pdbuchan/buscard/docs/assets/gerber/PLEASE_CHAMFER_CARD_EDGES.jpg

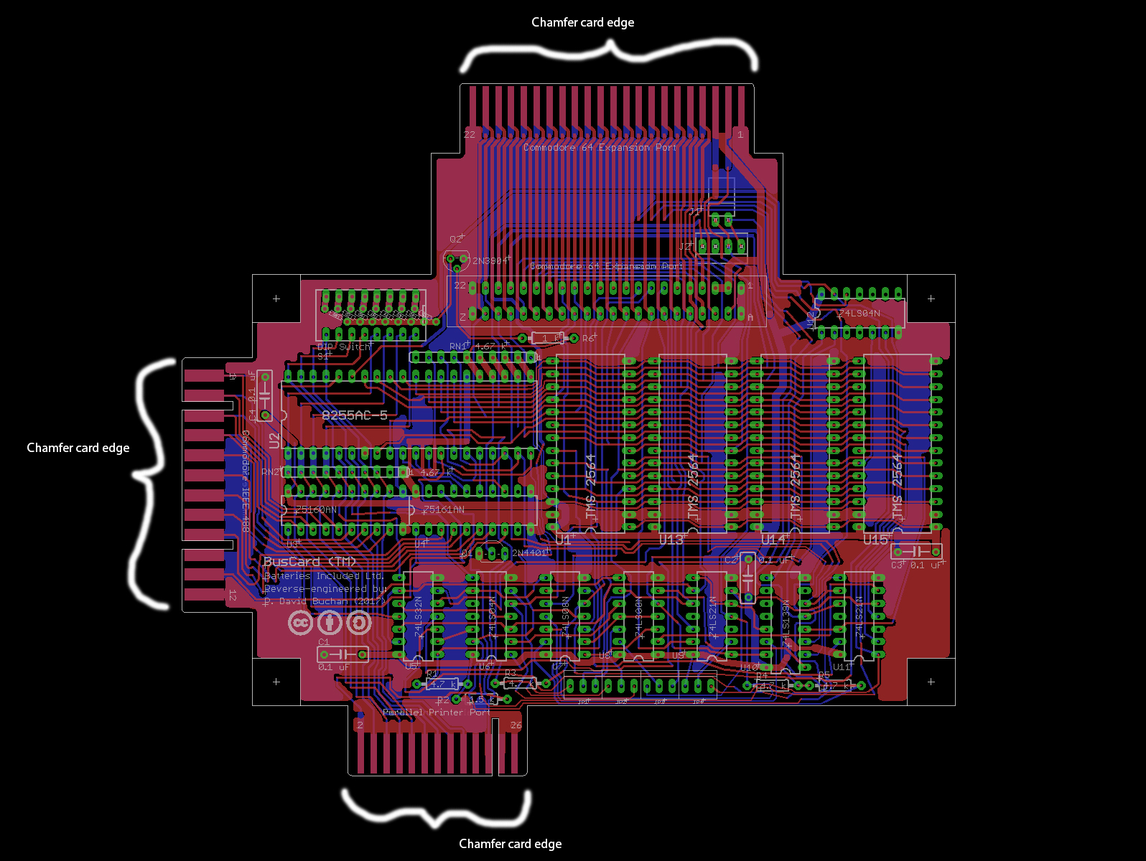
docs/assets/gerber/PLEASE_CHAMFER_CARD_EDGES.jpg
