pdbuchan/buscard/docs/assets/images/bottom.jpg

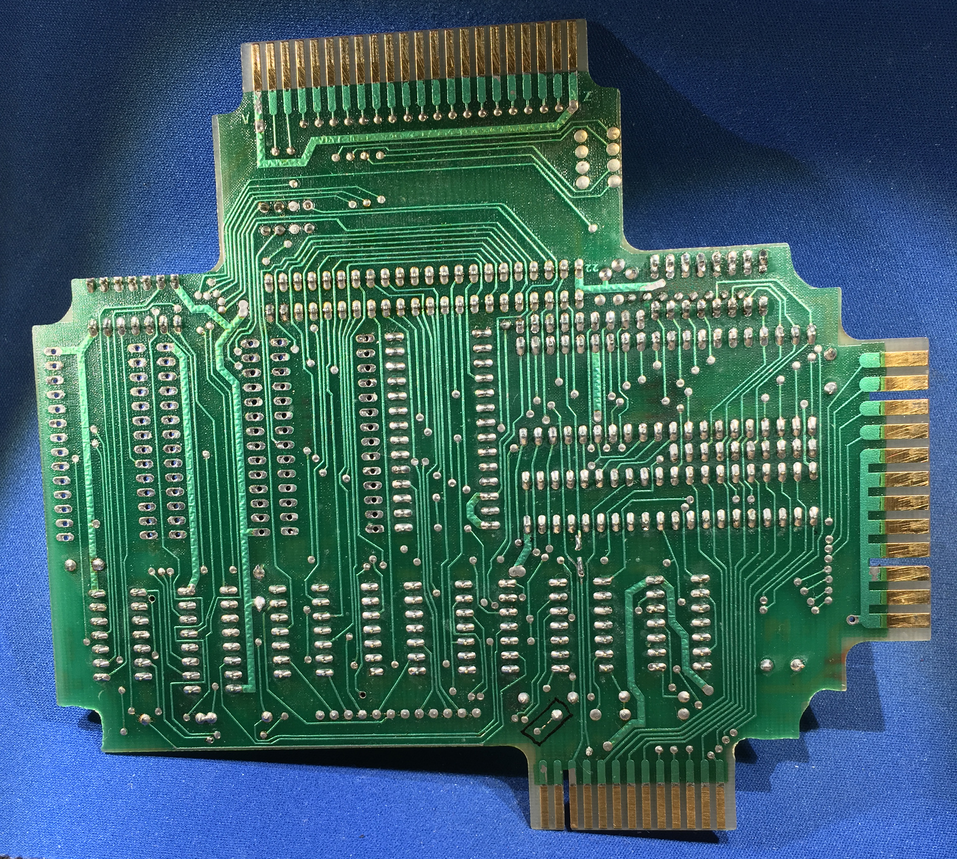
docs/assets/images/bottom.jpg
