pdbuchan/buscard/docs/assets/images/bottom_cover_inside.jpg

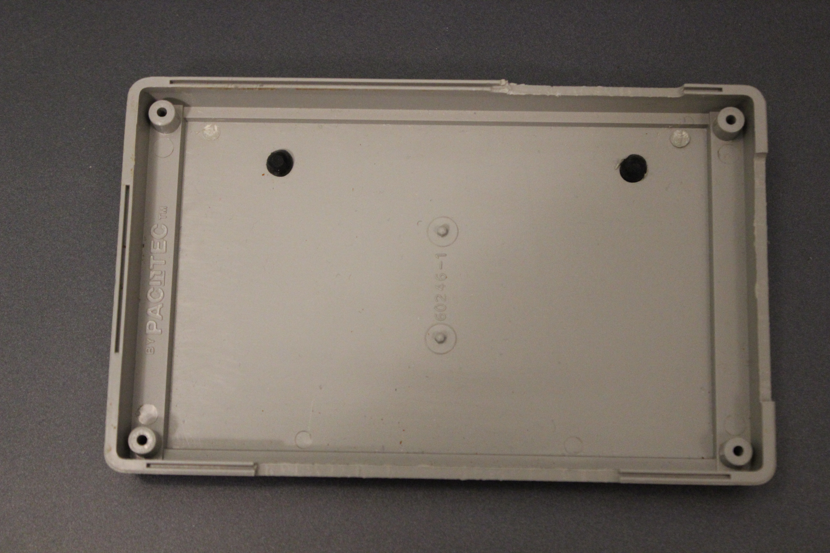
docs/assets/images/bottom_cover_inside.jpg
