pdbuchan/buscard/docs/assets/images/bottom_cover_underside.jpg

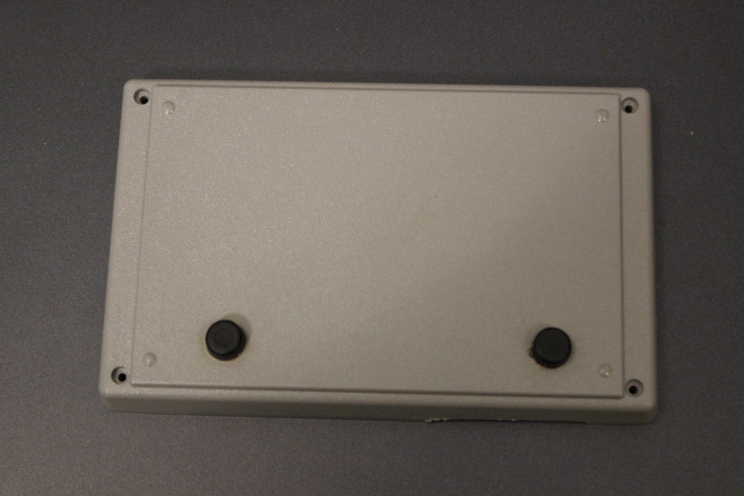
docs/assets/images/bottom_cover_underside.jpg
