pdbuchan/buscard/docs/assets/images/bottom_of_board_backlit.jpg

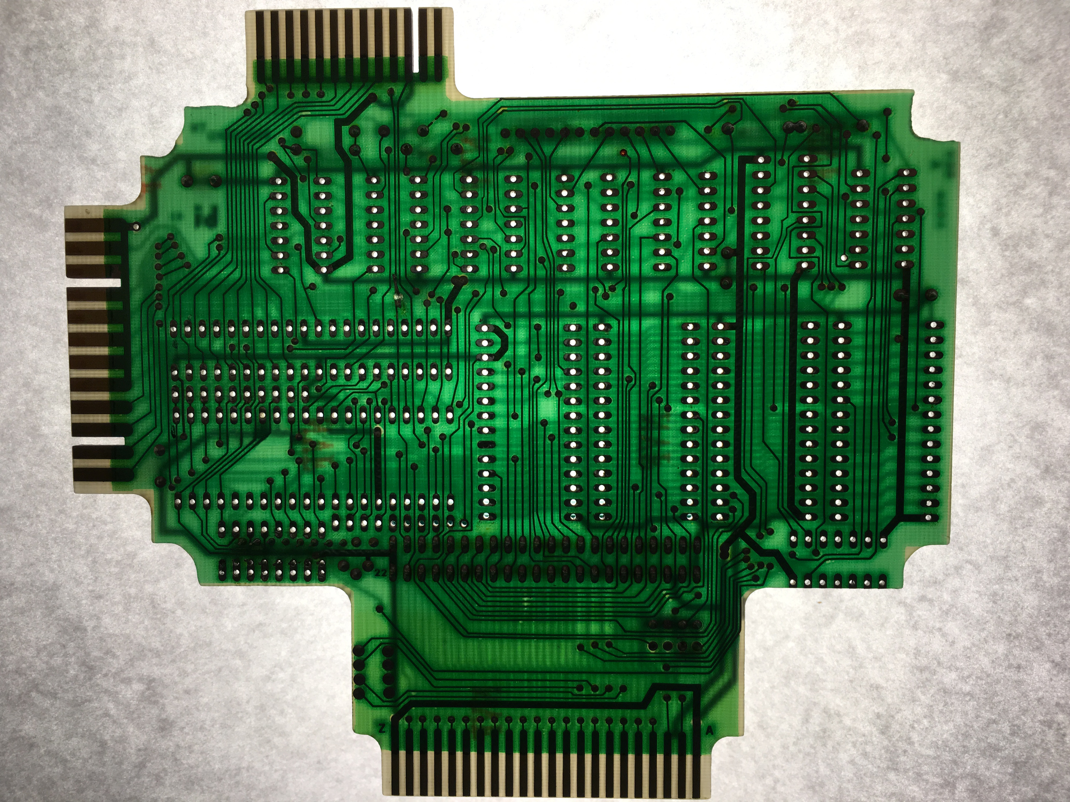
docs/assets/images/bottom_of_board_backlit.jpg
