pdbuchan/buscard/docs/assets/images/clips.jpg

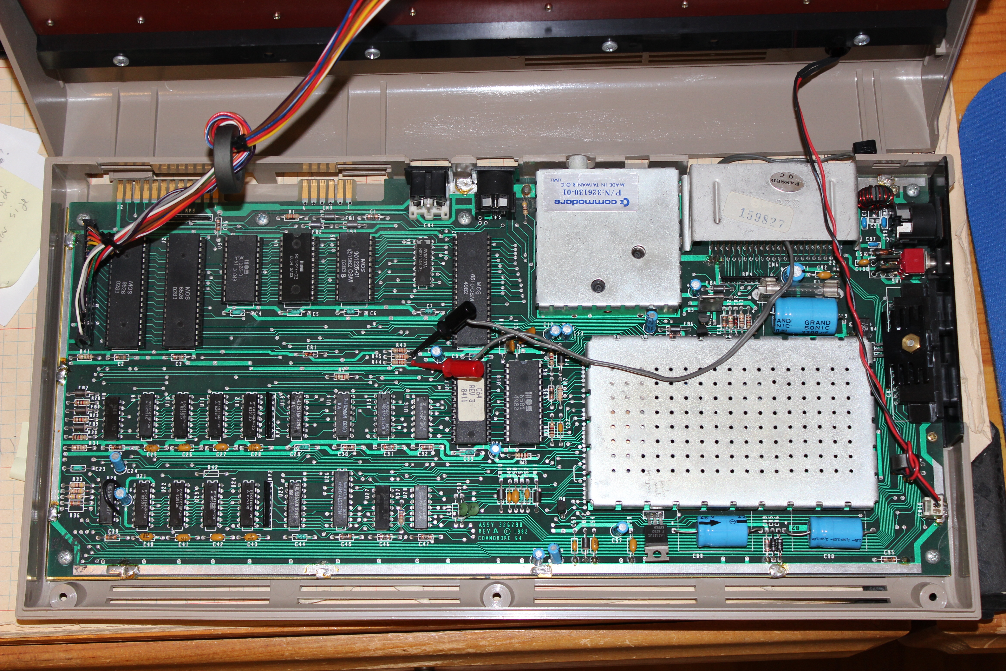
docs/assets/images/clips.jpg
