pdbuchan/buscard/docs/assets/images/diodes-switch_foil_backlit_top.jpg

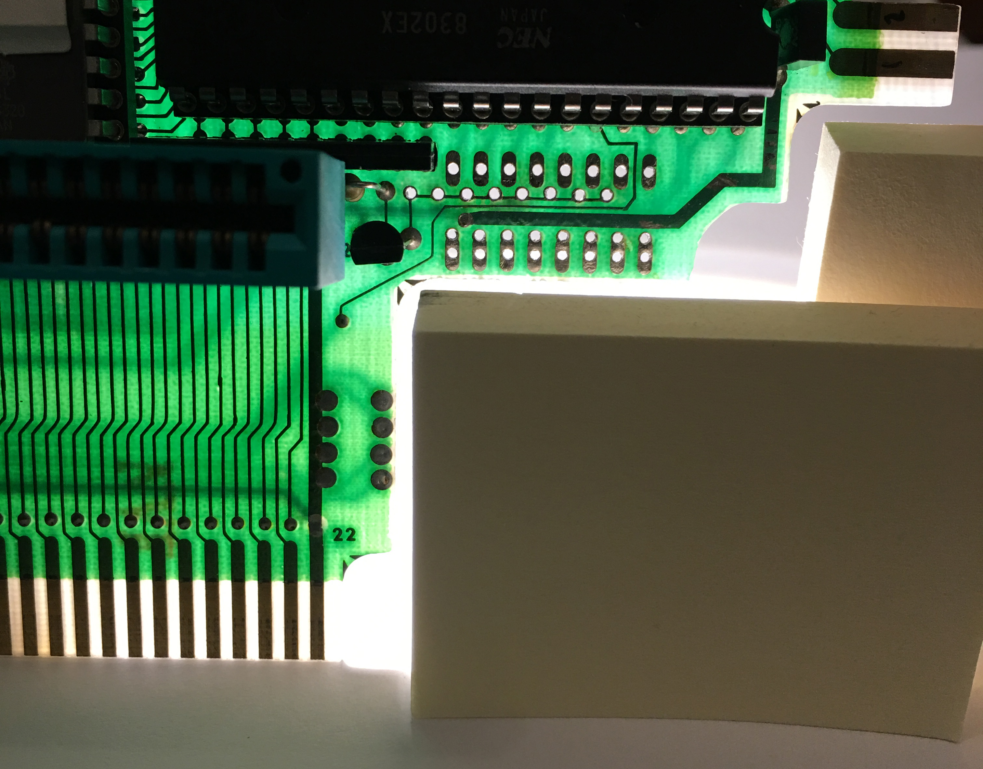
docs/assets/images/diodes-switch_foil_backlit_top.jpg
