pdbuchan/buscard/docs/assets/images/diodes-switch_foil_top.jpg

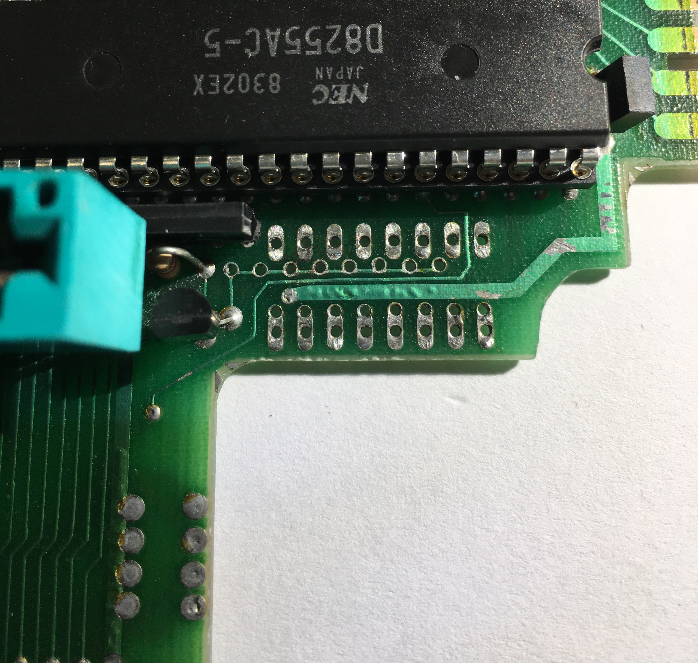
docs/assets/images/diodes-switch_foil_top.jpg
