pdbuchan/buscard/docs/assets/images/diodes.jpg

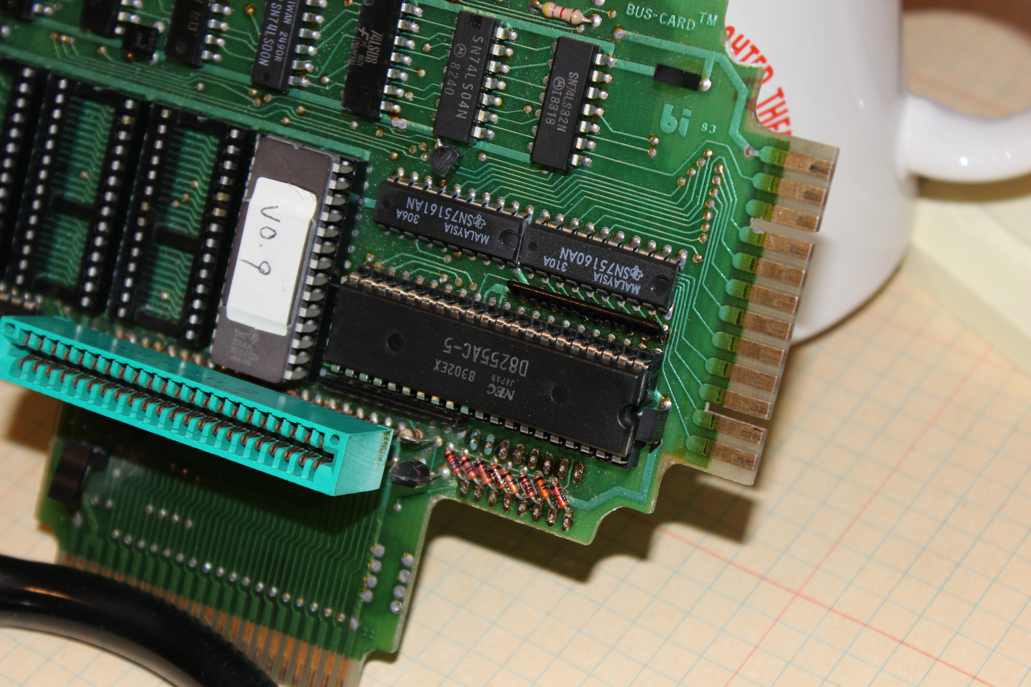
docs/assets/images/diodes.jpg
