pdbuchan/buscard/docs/assets/images/expansion_port_backlit1.jpg

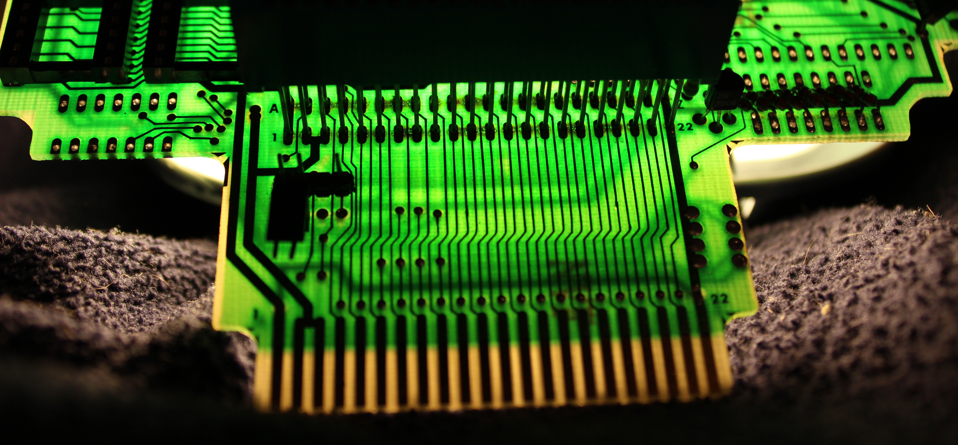
docs/assets/images/expansion_port_backlit1.jpg
