pdbuchan/buscard/docs/assets/images/expansion_port_backlit2.jpg

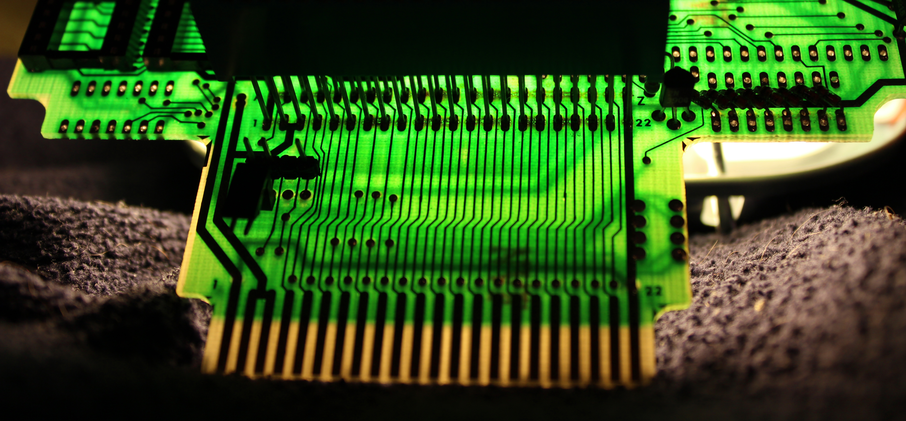
docs/assets/images/expansion_port_backlit2.jpg
