pdbuchan/buscard/docs/assets/images/new_bottom.jpg

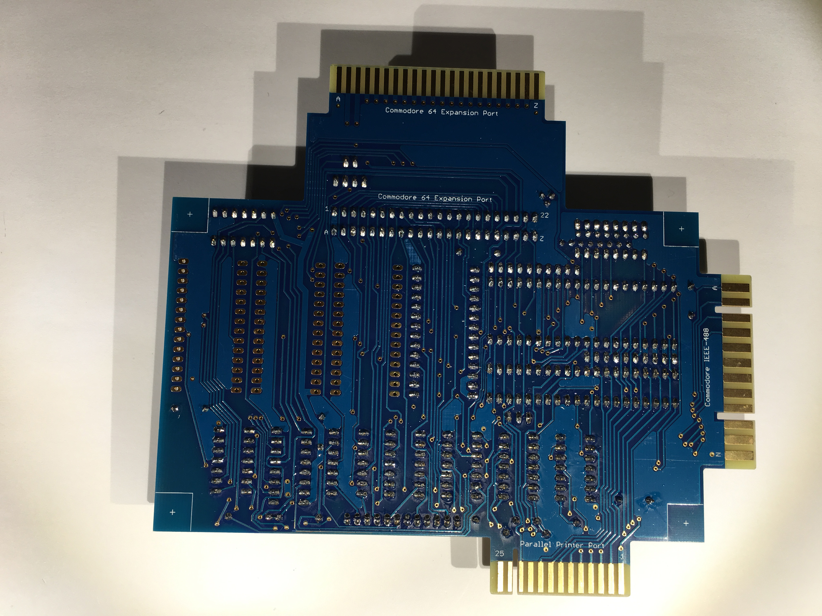
docs/assets/images/new_bottom.jpg
