pdbuchan/buscard/docs/assets/images/new_top1.jpg

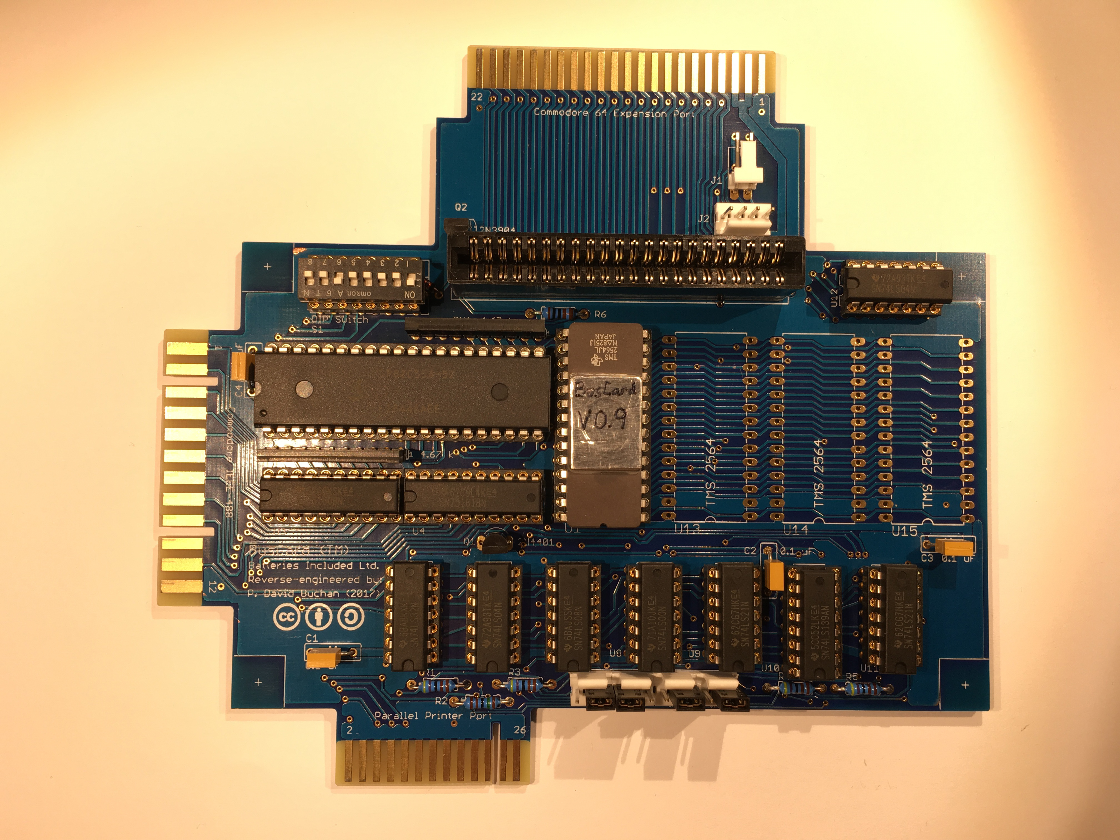
docs/assets/images/new_top1.jpg
