pdbuchan/buscard/docs/assets/images/new_top2.jpg

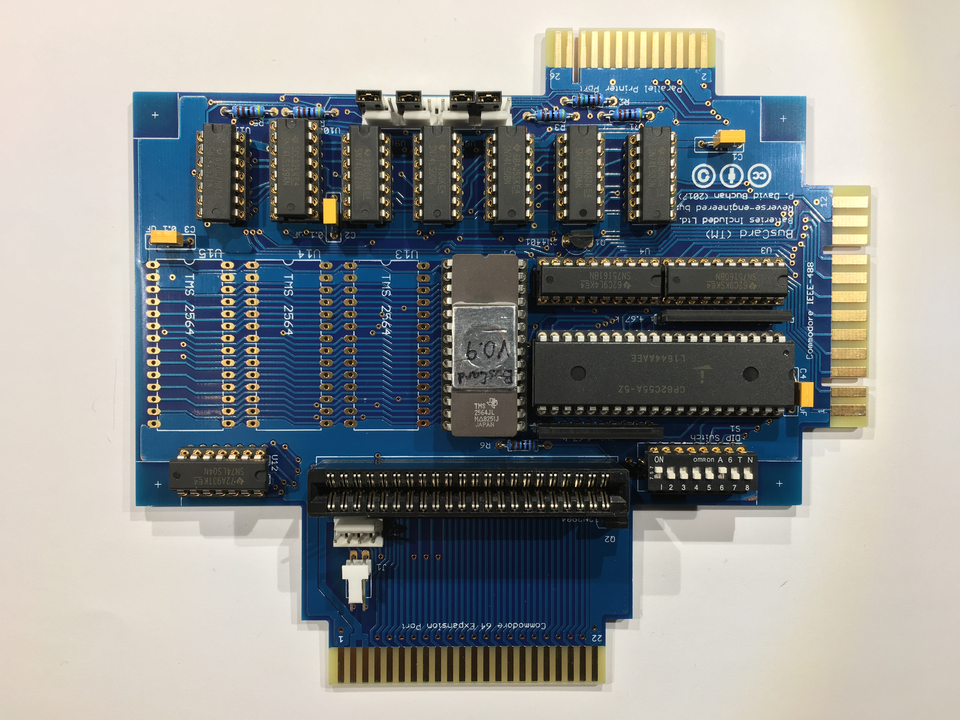
docs/assets/images/new_top2.jpg
