pdbuchan/buscard/docs/assets/images/new_top_no_chips1.jpg

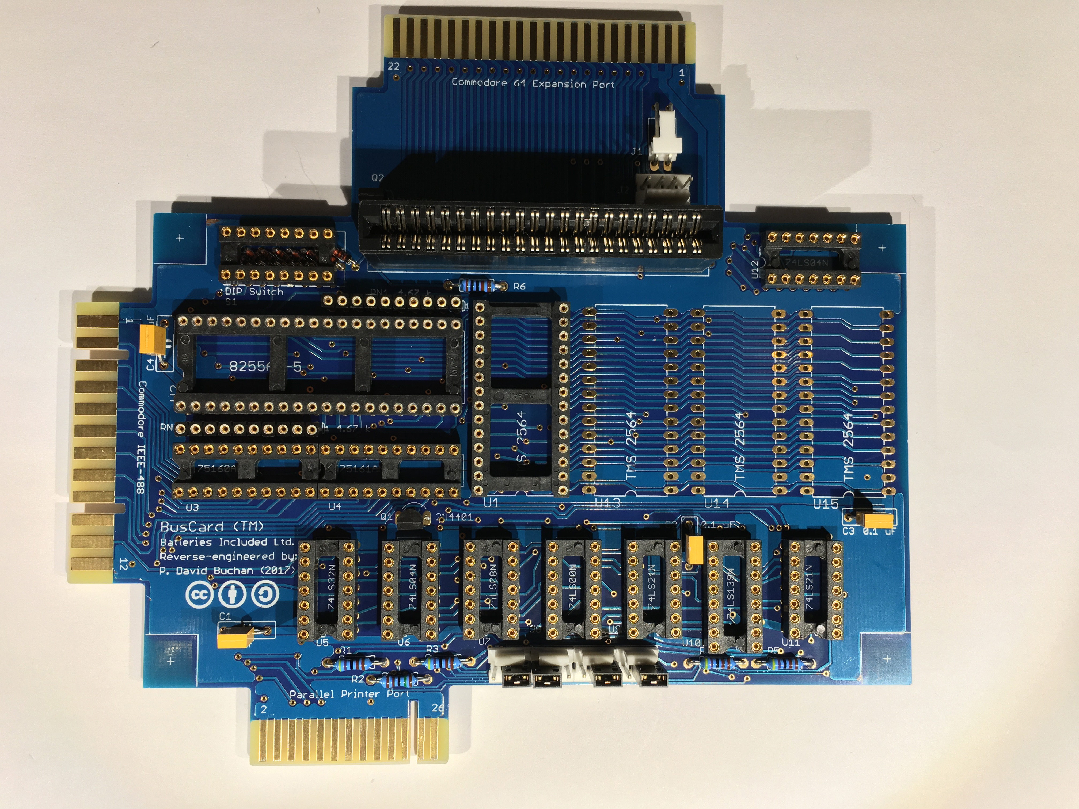
docs/assets/images/new_top_no_chips1.jpg
