pdbuchan/buscard/docs/assets/images/new_top_no_chips2.jpg

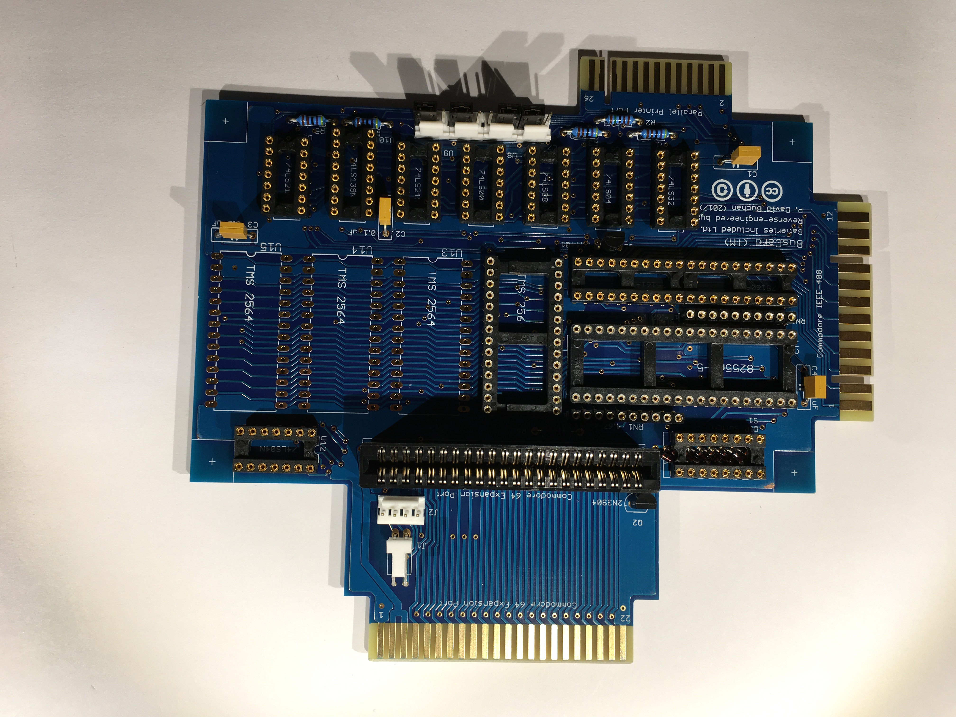
docs/assets/images/new_top_no_chips2.jpg
