pdbuchan/buscard/docs/assets/images/not_plugged_in.jpg

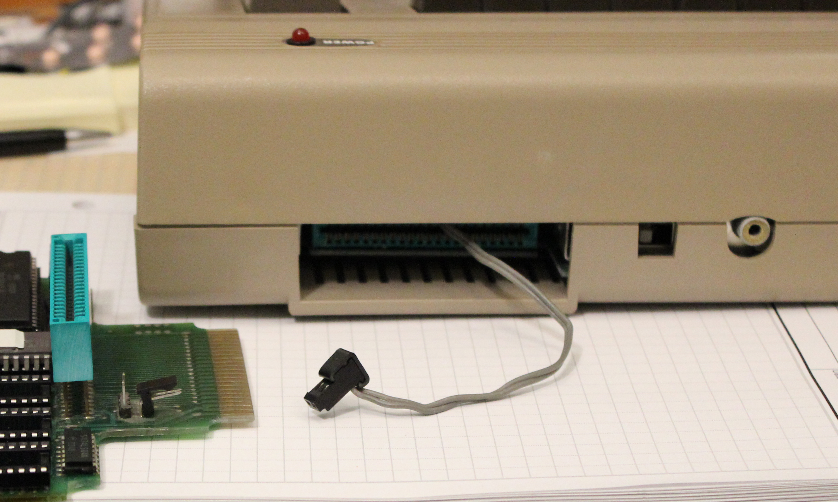
docs/assets/images/not_plugged_in.jpg
