pdbuchan/buscard/docs/assets/images/plugged_in.jpg

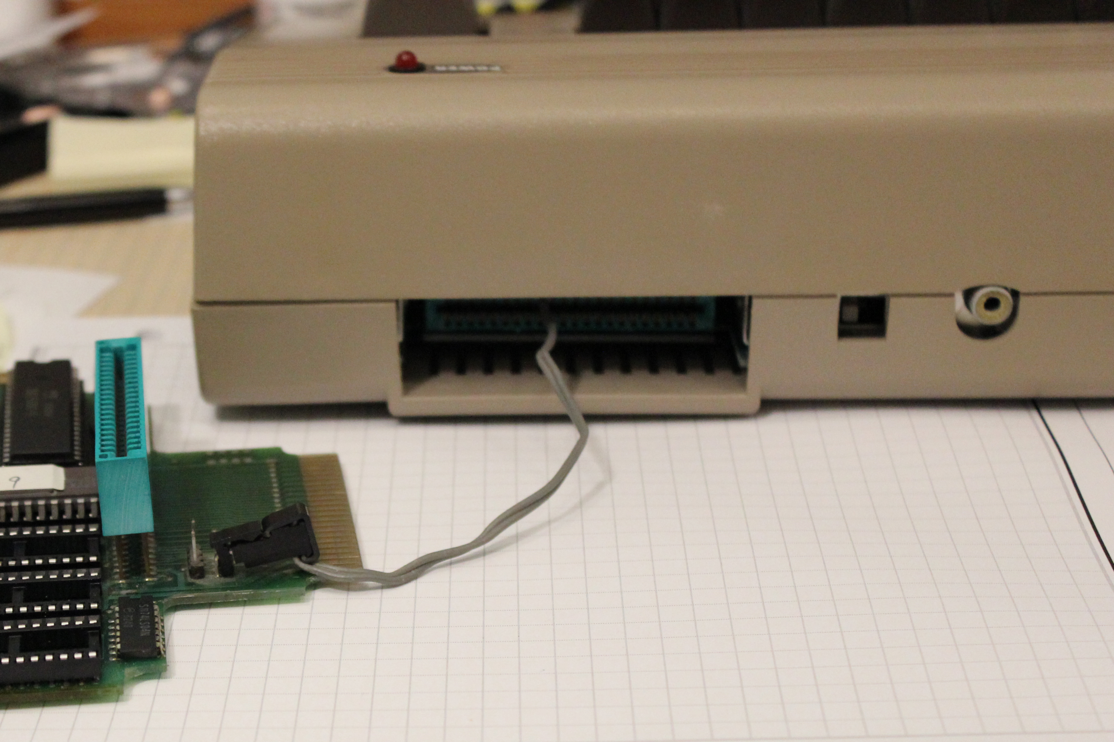
docs/assets/images/plugged_in.jpg
