pdbuchan/buscard/docs/assets/images/side_view01.jpg

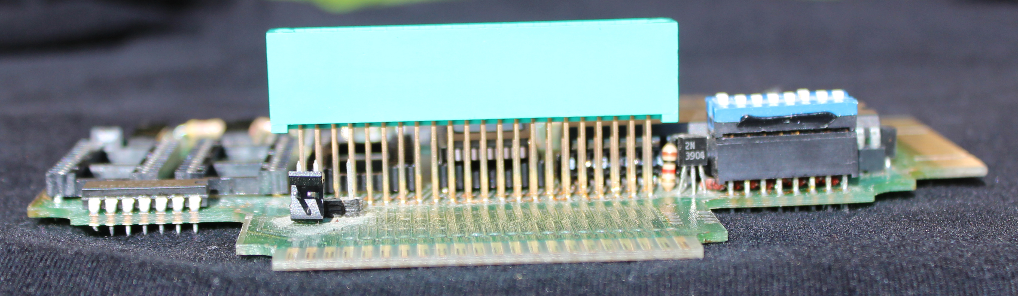
docs/assets/images/side_view01.jpg
