pdbuchan/buscard/docs/assets/images/side_view02.jpg

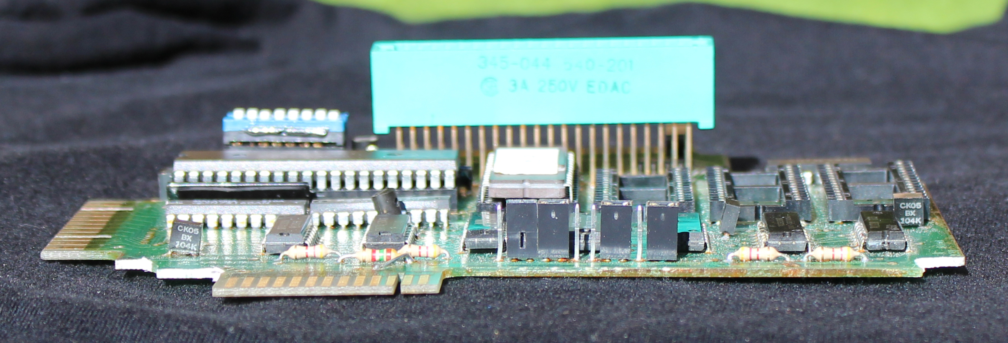
docs/assets/images/side_view02.jpg
