pdbuchan/buscard/docs/assets/images/side_view04.jpg

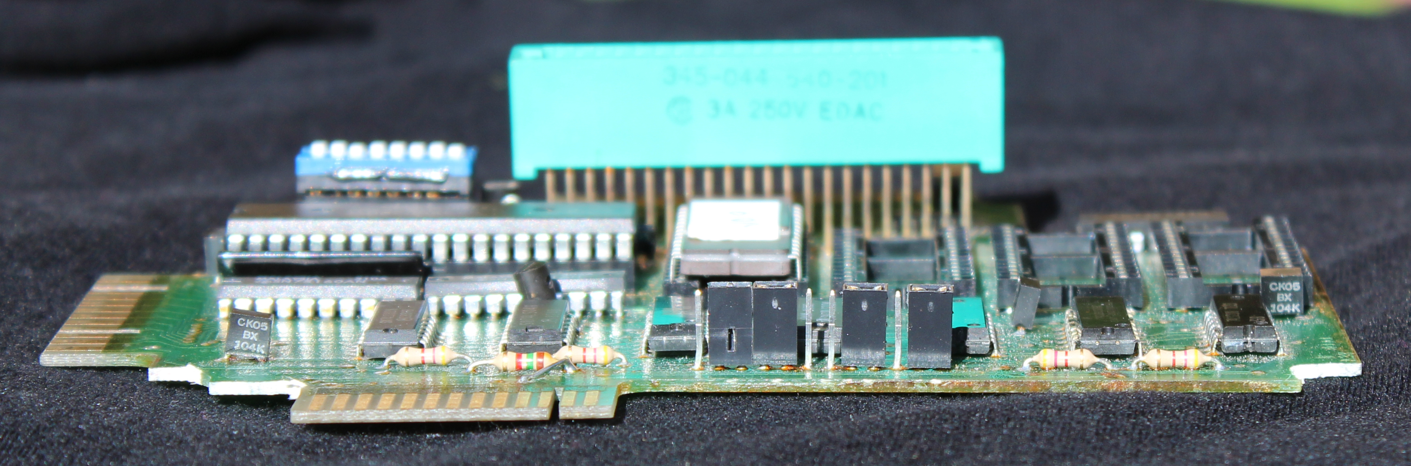
docs/assets/images/side_view04.jpg
