pdbuchan/buscard/docs/assets/images/side_view05.jpg

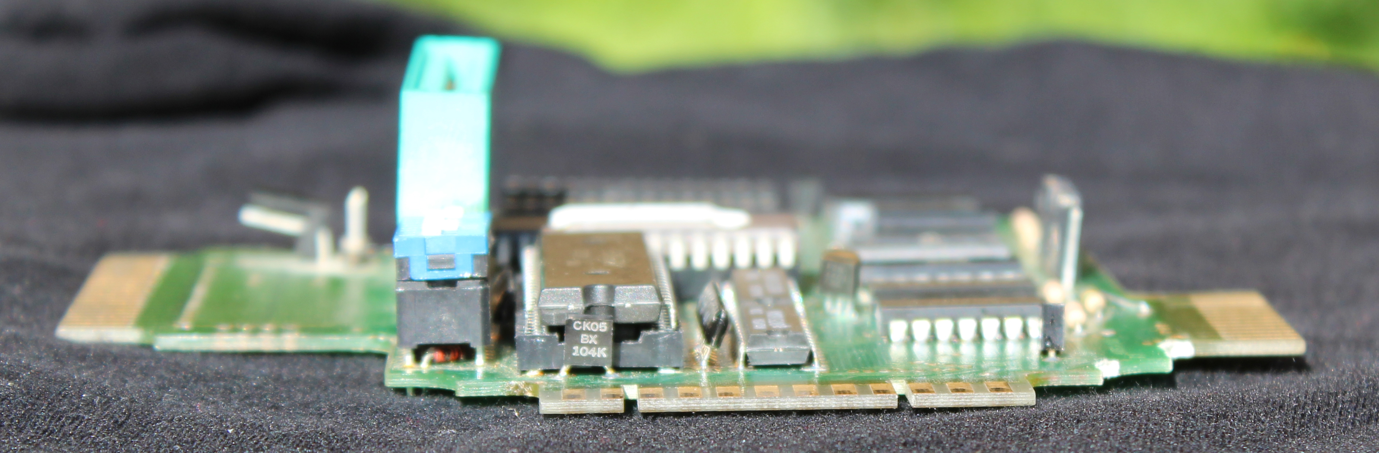
docs/assets/images/side_view05.jpg
