pdbuchan/buscard/docs/assets/images/side_view06.jpg

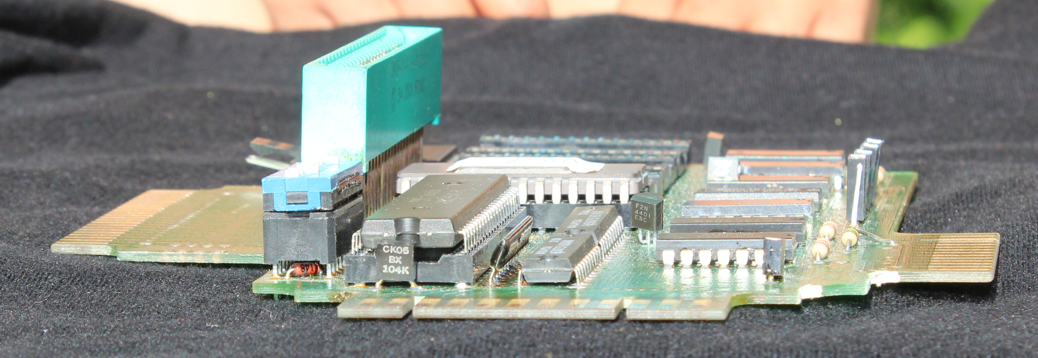
docs/assets/images/side_view06.jpg
