pdbuchan/buscard/docs/assets/images/side_view07.jpg

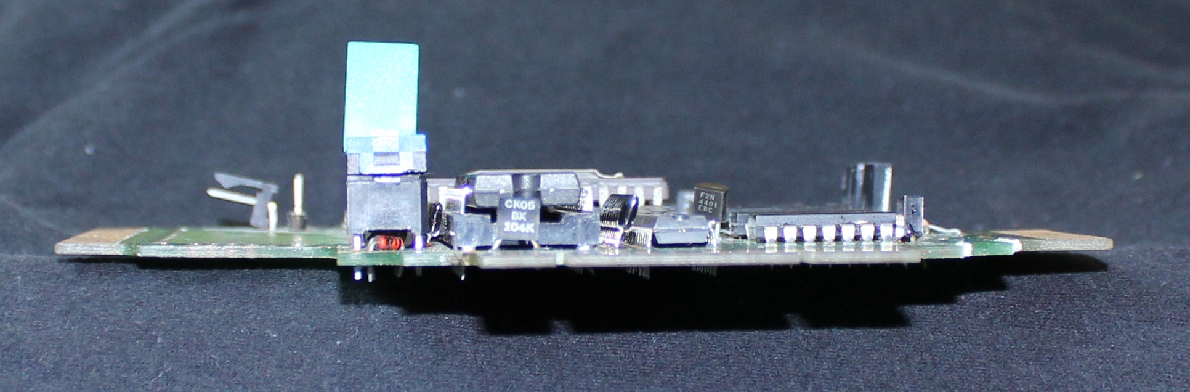
docs/assets/images/side_view07.jpg
