pdbuchan/buscard/docs/assets/images/side_view08.jpg

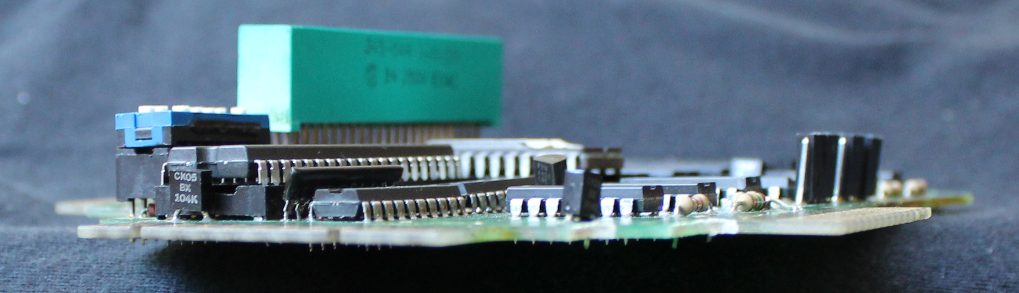
docs/assets/images/side_view08.jpg
