pdbuchan/buscard/docs/assets/images/side_view09.jpg

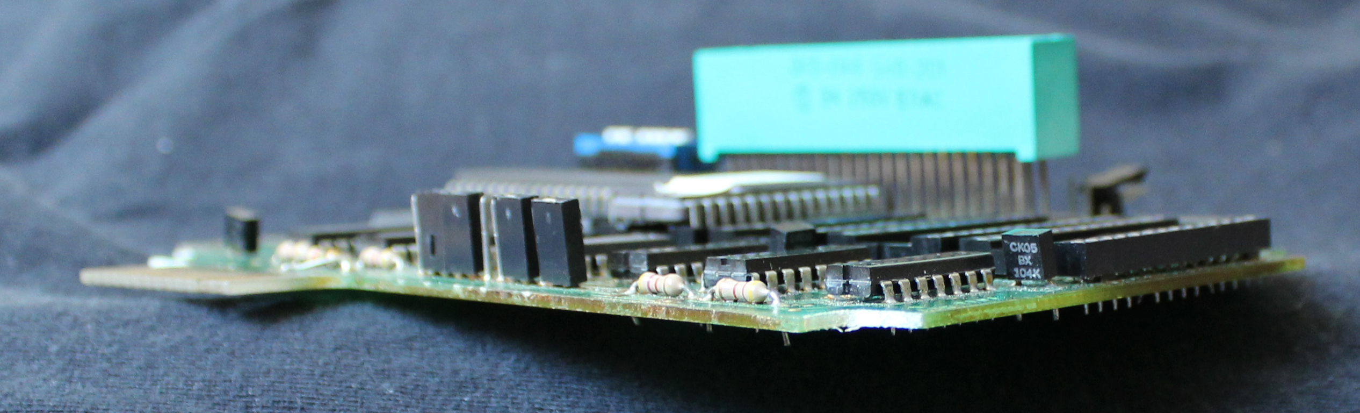
docs/assets/images/side_view09.jpg
