pdbuchan/buscard/docs/assets/images/side_view10.jpg

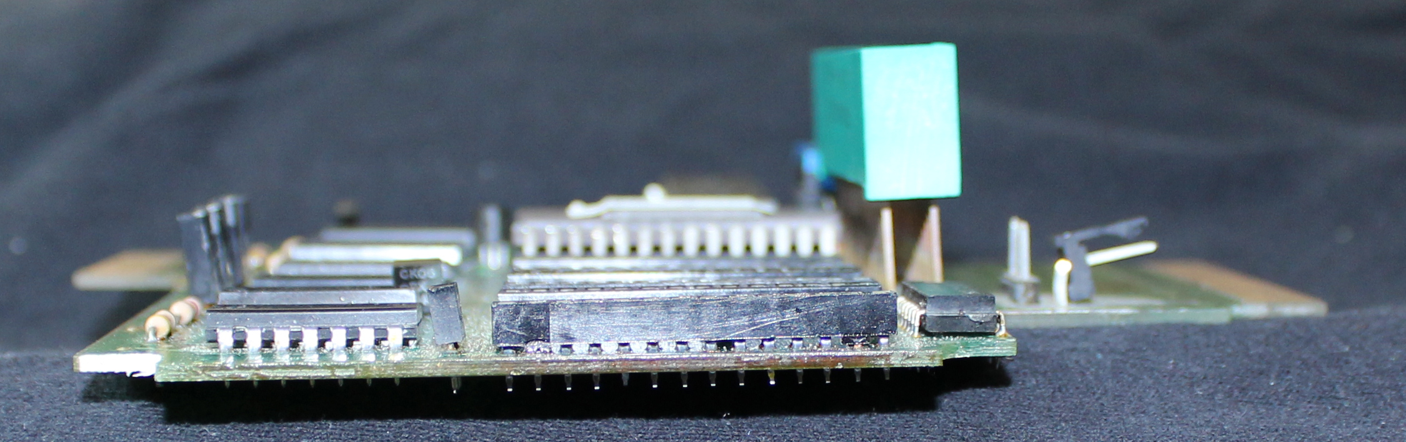
docs/assets/images/side_view10.jpg
