pdbuchan/buscard/docs/assets/images/side_view11.jpg

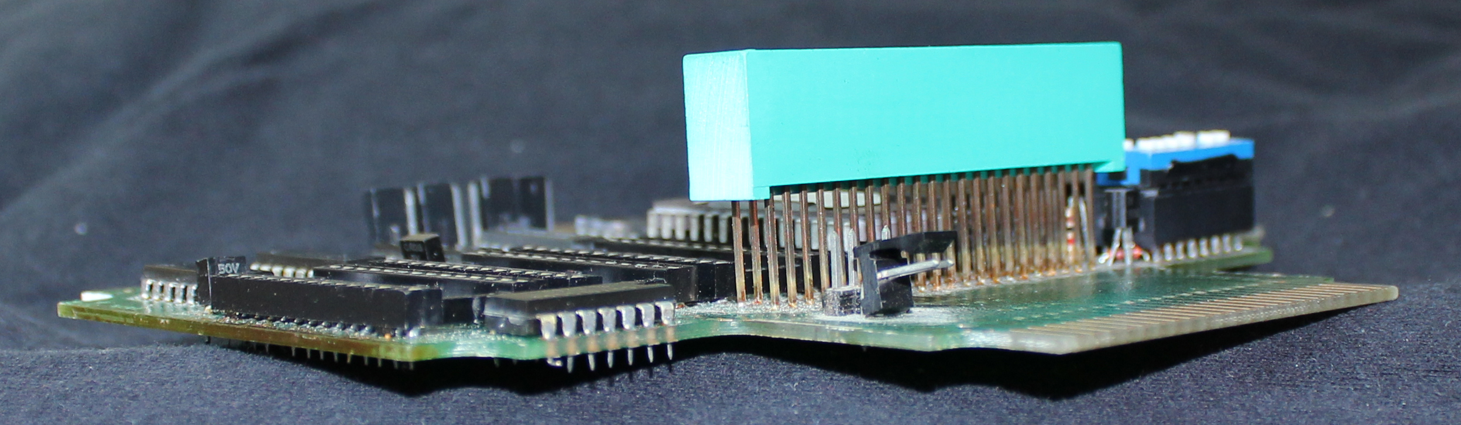
docs/assets/images/side_view11.jpg
