pdbuchan/buscard/docs/assets/images/side_view12.jpg

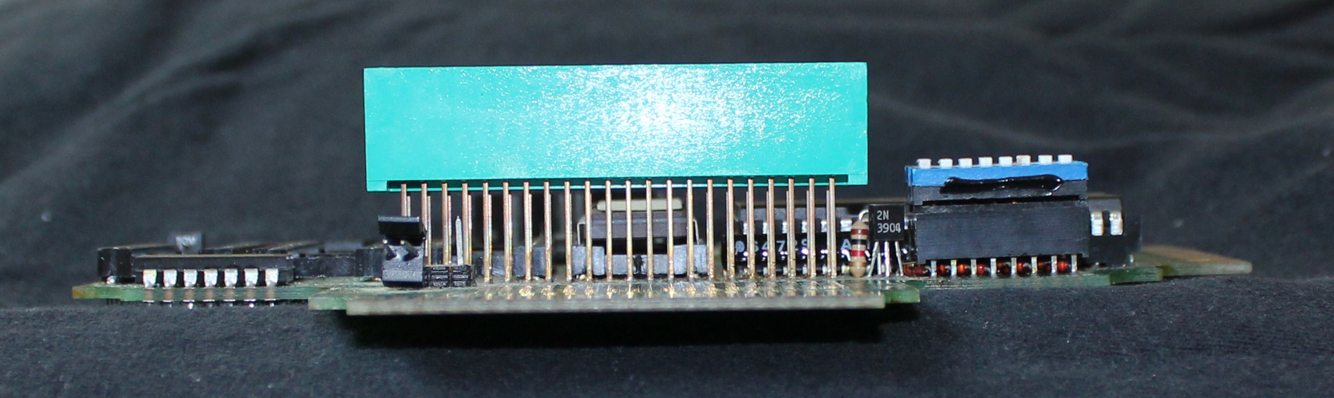
docs/assets/images/side_view12.jpg
