pdbuchan/buscard/docs/assets/images/side_view13.jpg

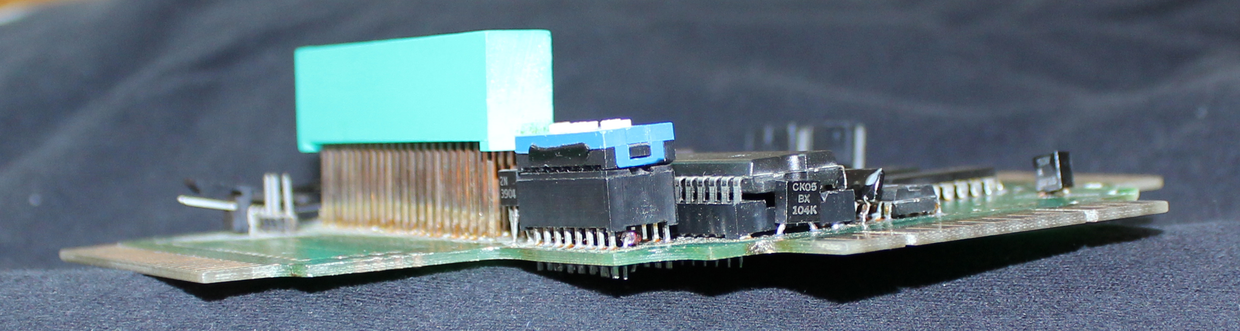
docs/assets/images/side_view13.jpg
