pdbuchan/buscard/docs/assets/images/top_cover_inside.jpg

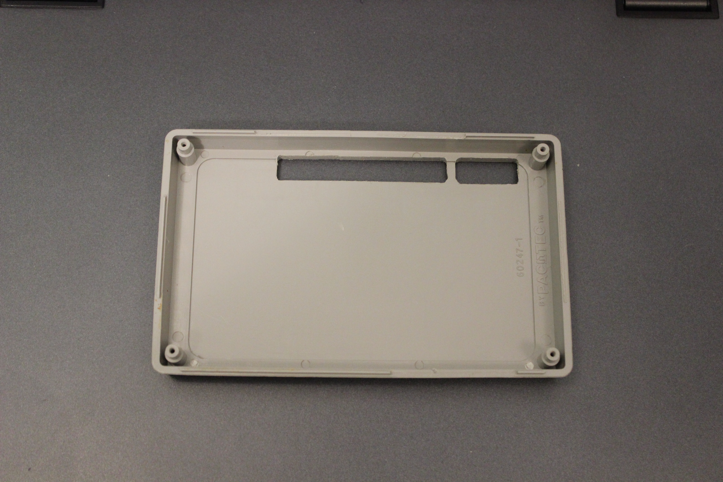
docs/assets/images/top_cover_inside.jpg
