pdbuchan/buscard/docs/assets/images/top_foil1.jpg

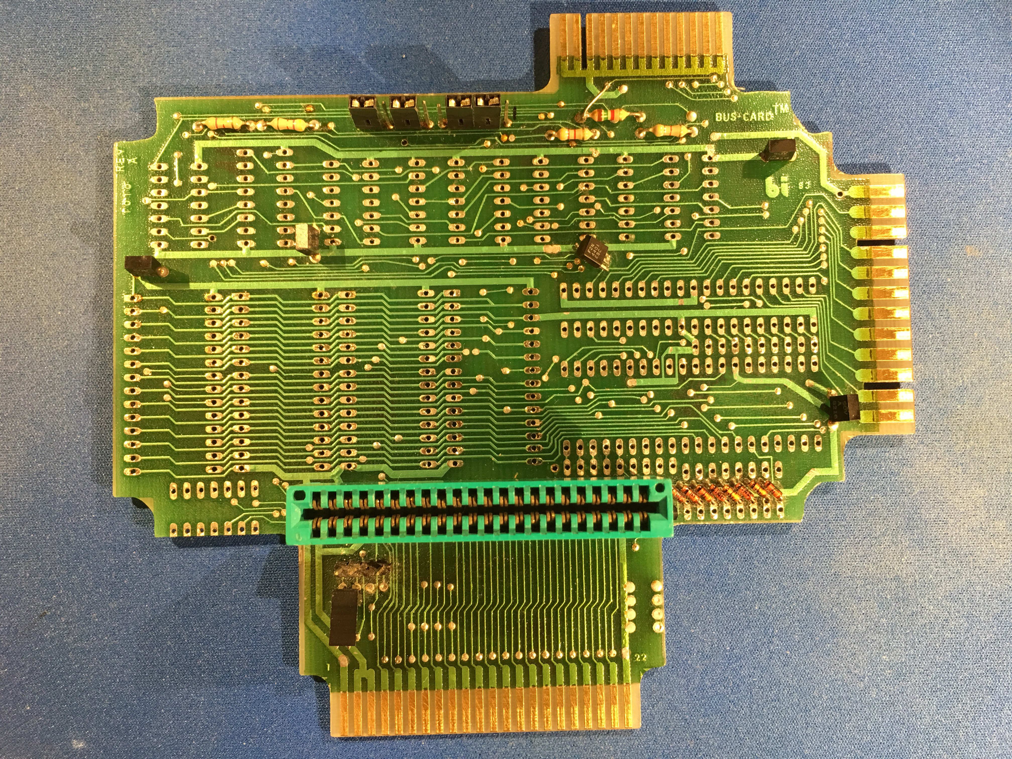
docs/assets/images/top_foil1.jpg
