pdbuchan/buscard/docs/assets/images/top_no_covers1.jpg

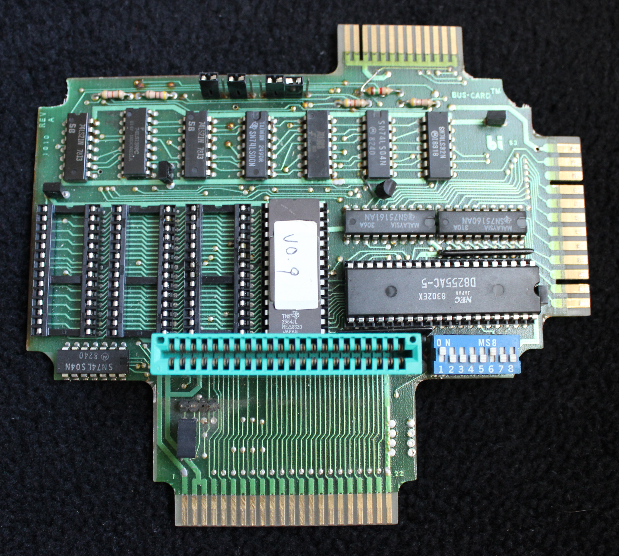
docs/assets/images/top_no_covers1.jpg
