pdbuchan/buscard/docs/assets/images/top_no_covers2.jpg

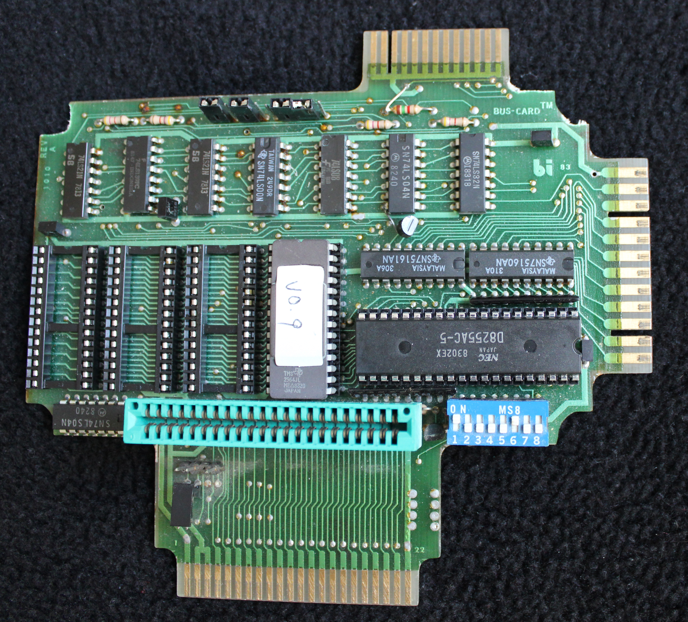
docs/assets/images/top_no_covers2.jpg
