pdbuchan/buscard/docs/assets/images/top_no_covers2_thumb.jpg

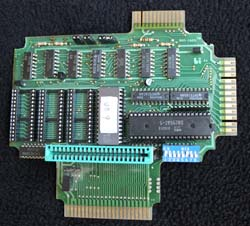
docs/assets/images/top_no_covers2_thumb.jpg
