pdbuchan/buscard/docs/assets/images/top_of_board_backlit.jpg

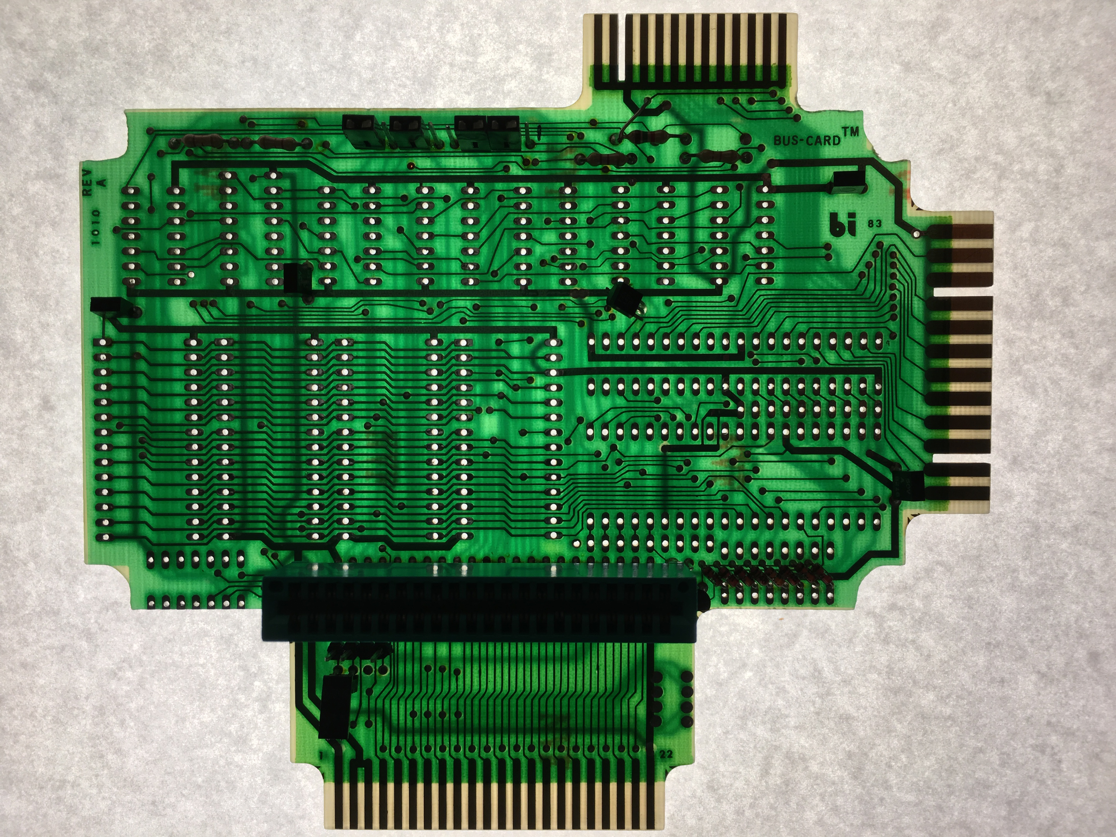
docs/assets/images/top_of_board_backlit.jpg
