pdbuchan/buscard/docs/assets/images/top_with_cover1.jpg

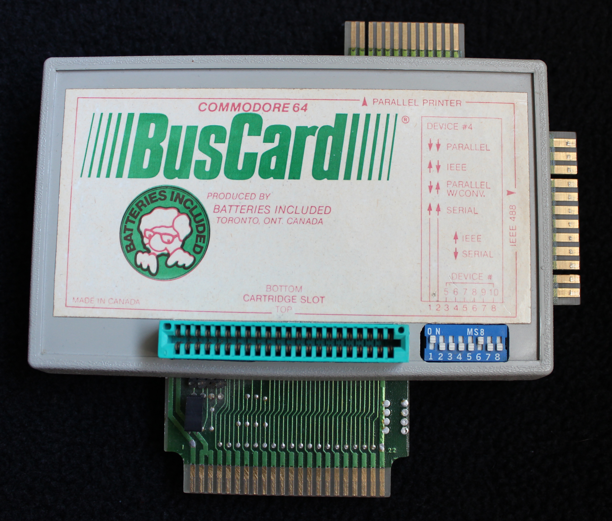
docs/assets/images/top_with_cover1.jpg
