pdbuchan/buscard/docs/assets/images/photo_buscard_board_bottom_r0.jpg

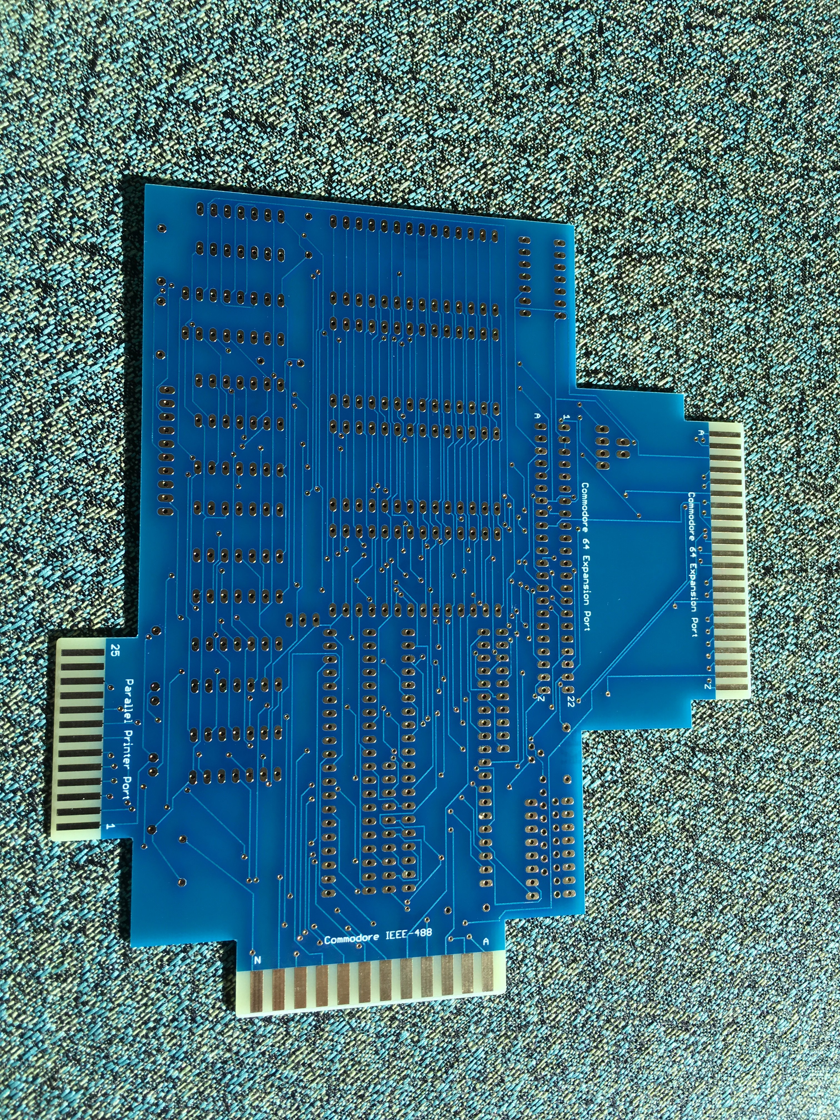
docs/assets/images/photo_buscard_board_bottom_r0.jpg
